rodan/gprs_i2c_gateway/hardware/ltspice/pwr_ctrl.asc

C1: cap; 10nF
C2: cap; 100nF
M1: pmos; IRF7233
Q1: npn; BC846B
Q2: npn; BC846B
R1: res; 1MEG
R2: res; 100k
R3: res; 1MEG
R4: res; 220K
R5: res; 25
V1: voltage; 13V; Rser=0.1
V2: voltage; PULSE(0 2.8V 1s 0.01 0.01 1s 2s)
Named nets: 0
.tran 0 4
